nickzentmayer/Messenger/data/assets/obackground.png

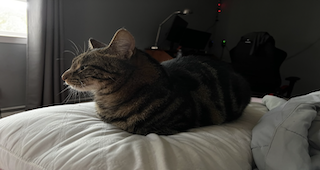
data/assets/obackground.png
