nickzentmayer/Messenger/data/assets/background.png

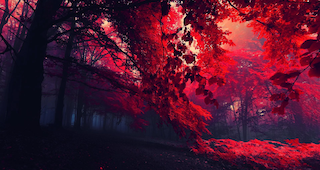
data/assets/background.png
